Jackadminx/KVM-Card-Mini/Client/SaveMedia/image_20230722-184414.jpg

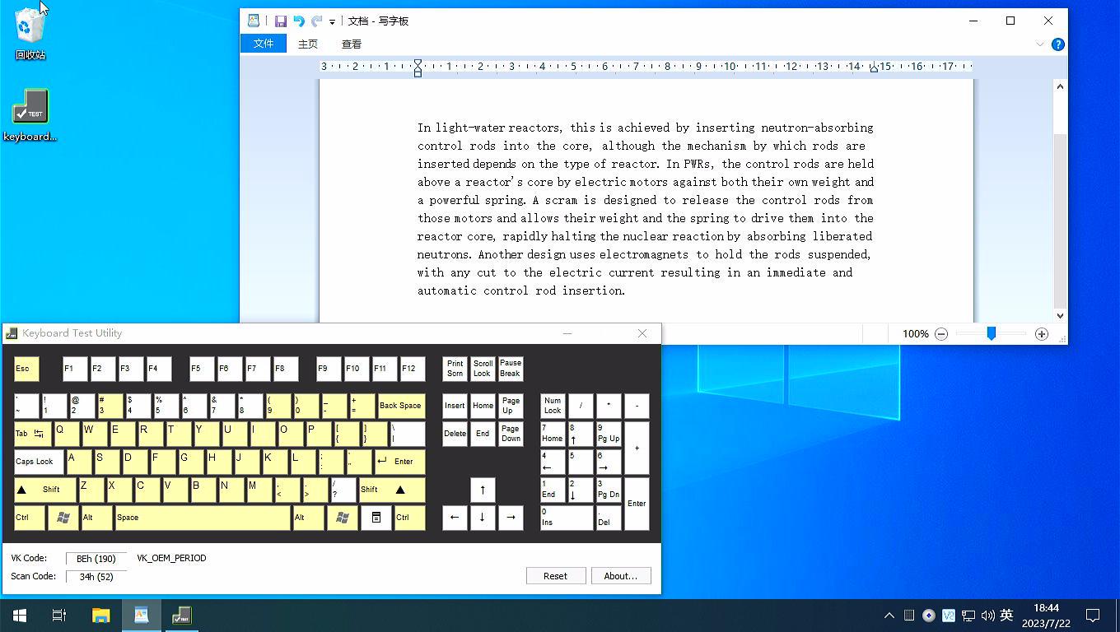
Client/SaveMedia/image_20230722-184414.jpg
