Jackadminx/KVM-Card-Mini/Document/Images/hv2.6-2.png

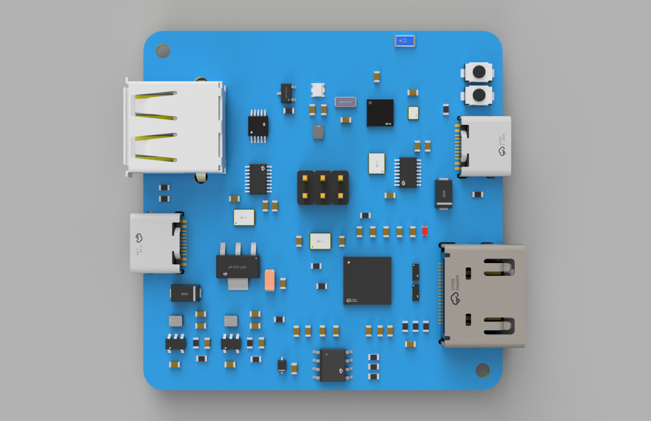
Document/Images/hv2.6-2.png
