Jackadminx/KVM-Card-Mini/Document/Images/IMG_1.jpg

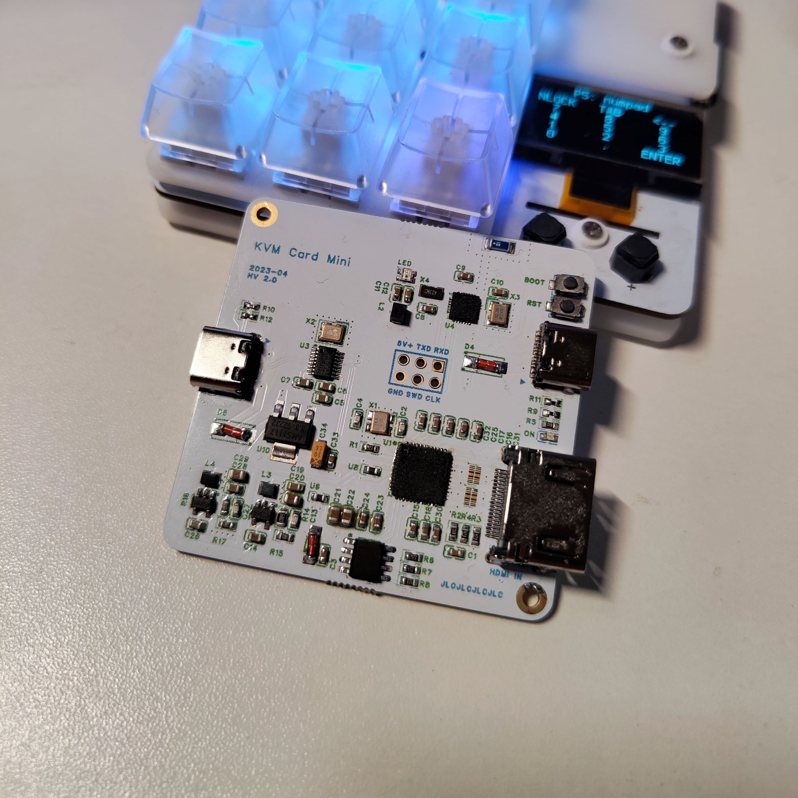
Document/Images/IMG_1.jpg
